calw20/MARS/src/fan_controllers/fan_controllers.cpp

#include "fan_controllers.h"

//Makes things look neater I guess?
bool FanController::init(){
    DBG_FPRINTLN("Initializing Fan Controllers...");
        marsRoot->data.transFanSpeed[1] = LOWER_SERVO_MAP; //These dont change
        marsRoot->data.transFanSpeed[2] = UPPER_SERVO_MAP;
        ESC.attach(ESC_PIN,1000,2000); //Init the ESC
    
    DBG_FPRINTLN("Arming Fan Controllers...");
        setSpeed(0);
    
    #if DO_DEBUG
        DBG_FPRINT("Please Wait");
            delay(400);
        DBG_FPRINT(".");
            delay(400);
        DBG_FPRINT(".");
            delay(400);
        DBG_FPRINT(".");
            delay(300);
    #else
        DBG_FPRINTLN("Please Wait...");
            delay(1500); //Wait for amring
    #endif
    DBG_FPRINTLN("Armed and Operational.");
    
    DBG_FPRINT("Initialized Fan Controllers.");

    return true;
}

void FanController::genericError(const char* func, const char* file, u16 failLine){
    DBG_FPRINTLN("################## Fan Controllers Error Info ##################");
    DBG_FPRINTF("The Fan Controllers have experienced an Error of type: ","[%s]\r\nMore Details;\r\n",
        CrashTypeText[status]); //DBG_PRINTLN();
    printErrorInfo(func, file, failLine);
    printDebug("-H");
    DBG_PRINTLN();
}

void FanController::printDebug(String printValues){
    //^ Defined in debug.h? //#define CHK_LETTER(letter) printValues.indexOf(letter) > -1
    if (CHK_LETTER("-H")) printValues = "I";

    if (CHK_LETTER("H")) DBG_FPRINTLN("===================== Fan Controllers Info =====================");
    
    if (CHK_LETTER("I")){
        DBG_FPRINT_SVLN("Current Fan Speed: ", currentSpeed);
        
    }
}

//The inverse of setSpeed; Returns a value from [LOWER_SERVO_MAP, UPPER_SERVO_MAP] in [lowerESCmap, upperESCmap]
int FanController::getSpeed(){
    return map(currentSpeed, LOWER_SERVO_MAP, UPPER_SERVO_MAP, lowerESCmap, upperESCmap);
}

void FanController::writeSpeed(){
    ESC.write(currentSpeed);
}

//Convert a value in [lowerESCmap, upperESCmap] to [LOWER_SERVO_MAP, UPPER_SERVO_MAP] for the Servo Lib
void FanController::setSpeed(int newSpeed){
    currentSpeed = map(newSpeed, lowerESCmap, upperESCmap, LOWER_SERVO_MAP, UPPER_SERVO_MAP);
    DBG_FPRINT_SVLN("New FanSpeed: ", currentSpeed);
    writeSpeed();
}


bool FanController::updatePayloadData(bool forceDataUpdate){
    marsRoot->data.transFanSpeed[0] = currentSpeed; 
    marsRoot->data.fanSpeed[0] = getSpeed();
        marsRoot->data.fanSpeed[1] = lowerESCmap;
        marsRoot->data.fanSpeed[2] = upperESCmap;
    return true;
}
