calw20/MARS/src/wireless_module/wireless_settings.h

#ifndef __MARS_WIRELESS_SETTINGS_H__
#define __MARS_WIRELESS_SETTINGS_H__

#define CE_PIN 49
#define CS_PIN 48
#define RADIOMODE 0

#ifndef RADIO_TIMEOUT
    #define RADIO_TIMEOUT 500UL //ms
#endif

#endif
